manhoosbilli1/heater-controller-rev-a/Images/HEATER CONTROLLER REV_A_Checked_prototype_v1.0_back.png

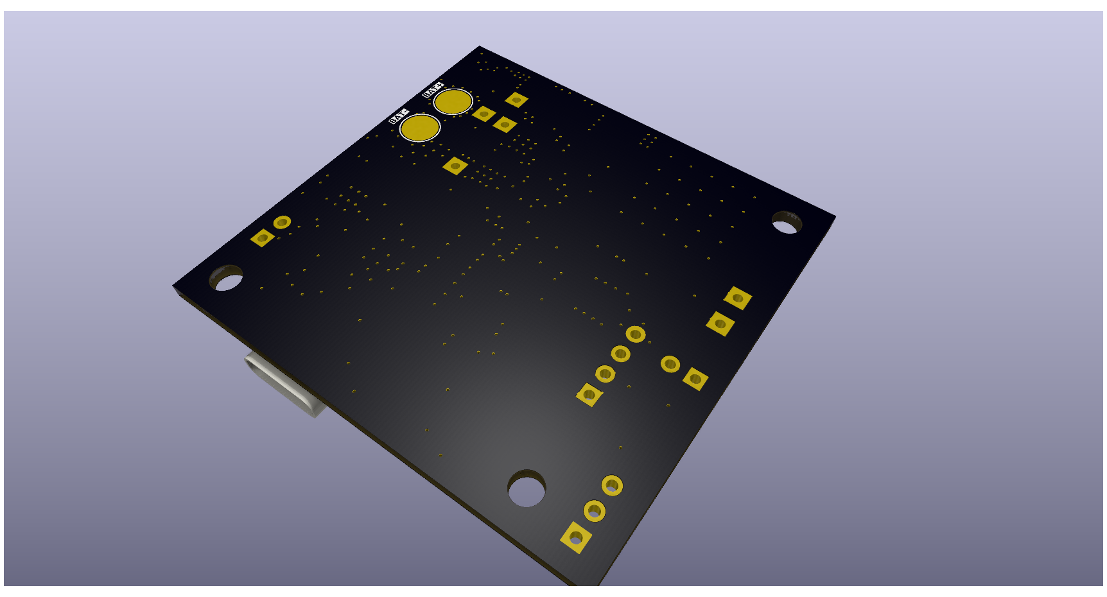
Images/HEATER CONTROLLER REV_A_Checked_prototype_v1.0_back.png
