manhoosbilli1/heater-controller-rev-a/Images/HEATER CONTROLLER REV_A_Checked_prototype_v1.0_front_copper_plane.png

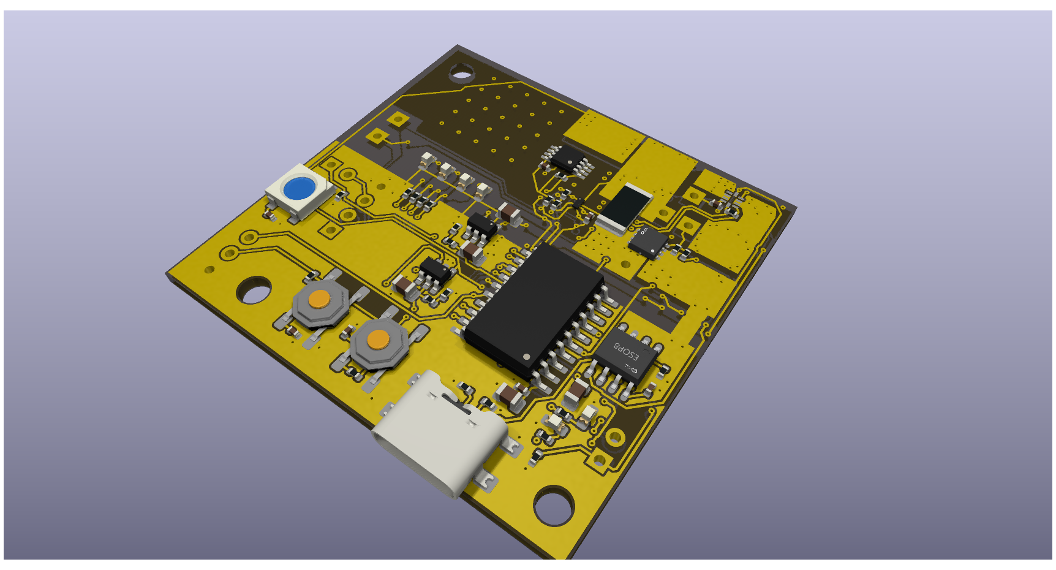
Images/HEATER CONTROLLER REV_A_Checked_prototype_v1.0_front_copper_plane.png
