manhoosbilli1/heater-controller-rev-a/Images/PRELIMINARY PLACEMENT BACK.png

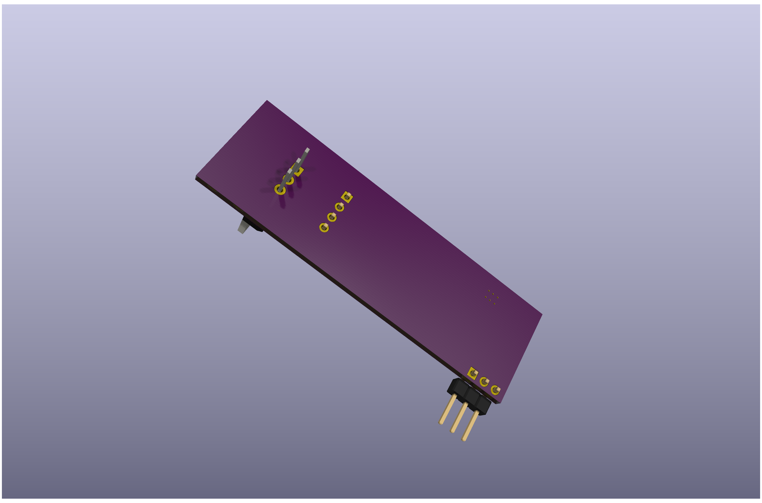
Images/PRELIMINARY PLACEMENT BACK.png
