manhoosbilli1/heater-controller-rev-a/Research/conductor_high_current_calculation.png

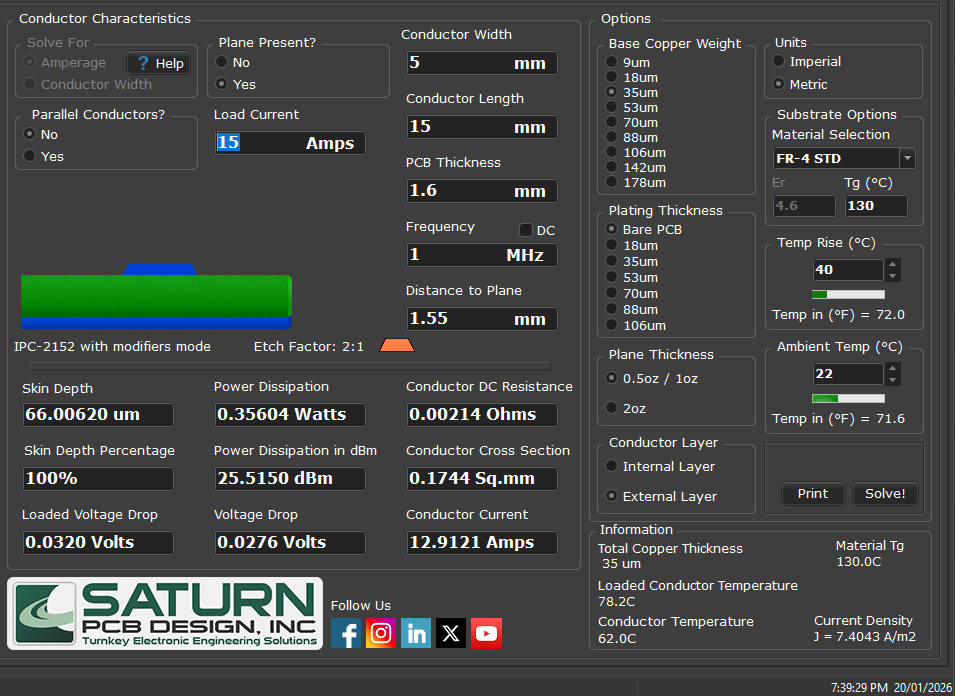
Research/conductor_high_current_calculation.png
